wirthual/smartkanne/docs/housing/RFID_inverted_scaled.jpg

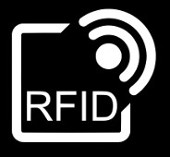
docs/housing/RFID_inverted_scaled.jpg
